ProrokWielki/Wooden-Clock/Hardware/Electronics/Schematic/ButtonBoard/ButtonBoard.kicad_sch

## KiCad design Hardware/Electronics/Schematic/ButtonBoard/ButtonBoard.kicad_sch (2025-12-02)

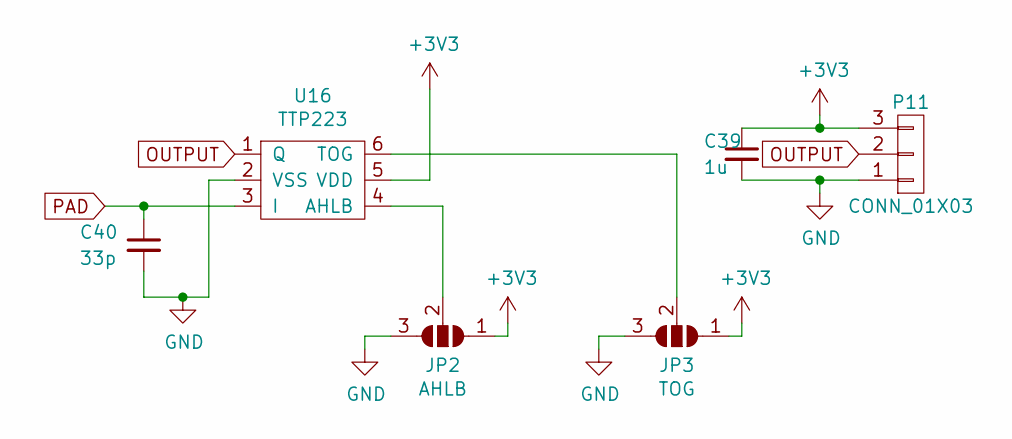
[picture p11: schematic ButtonBoard.kicad_sch]

Parts:
C39: 1u; C_0402_1005Metric
C40: 33p; C_0402_1005Metric
JP2: AHLB; SolderJumper-3_P1.3mm_Open_RoundedPad1.0x1.5mm
JP3: TOG; SolderJumper-3_P1.3mm_Open_RoundedPad1.0x1.5mm
P11: CONN_01X03; Molex_CLIK-Mate_502382-0370_1x03-1MP_P1.25mm_Vertical
U16: TTP223; SOT-23-6

Connections:
+3V3: C39.1, JP2.1 (A), JP3.1 (A), P11.3, U16.5 (VDD)
GND: C39.2, C40.2, JP2.3 (B), JP3.3 (B), P11.1, U16.2 (VSS)
unnamed: JP2.2 (C), U16.4 (AHLB)
unnamed: JP3.2 (C), U16.6 (TOG)
OUTPUT: P11.2, U16.1 (Q)
PAD: C40.1, U16.3 (I)
