ProrokWielki/Wooden-Clock/Hardware/Electronics/Schematic/DisplayBoard/DisplayBoard.kicad_sch

## KiCad design Hardware/Electronics/Schematic/DisplayBoard/DisplayBoard.kicad_sch (2025-12-02)

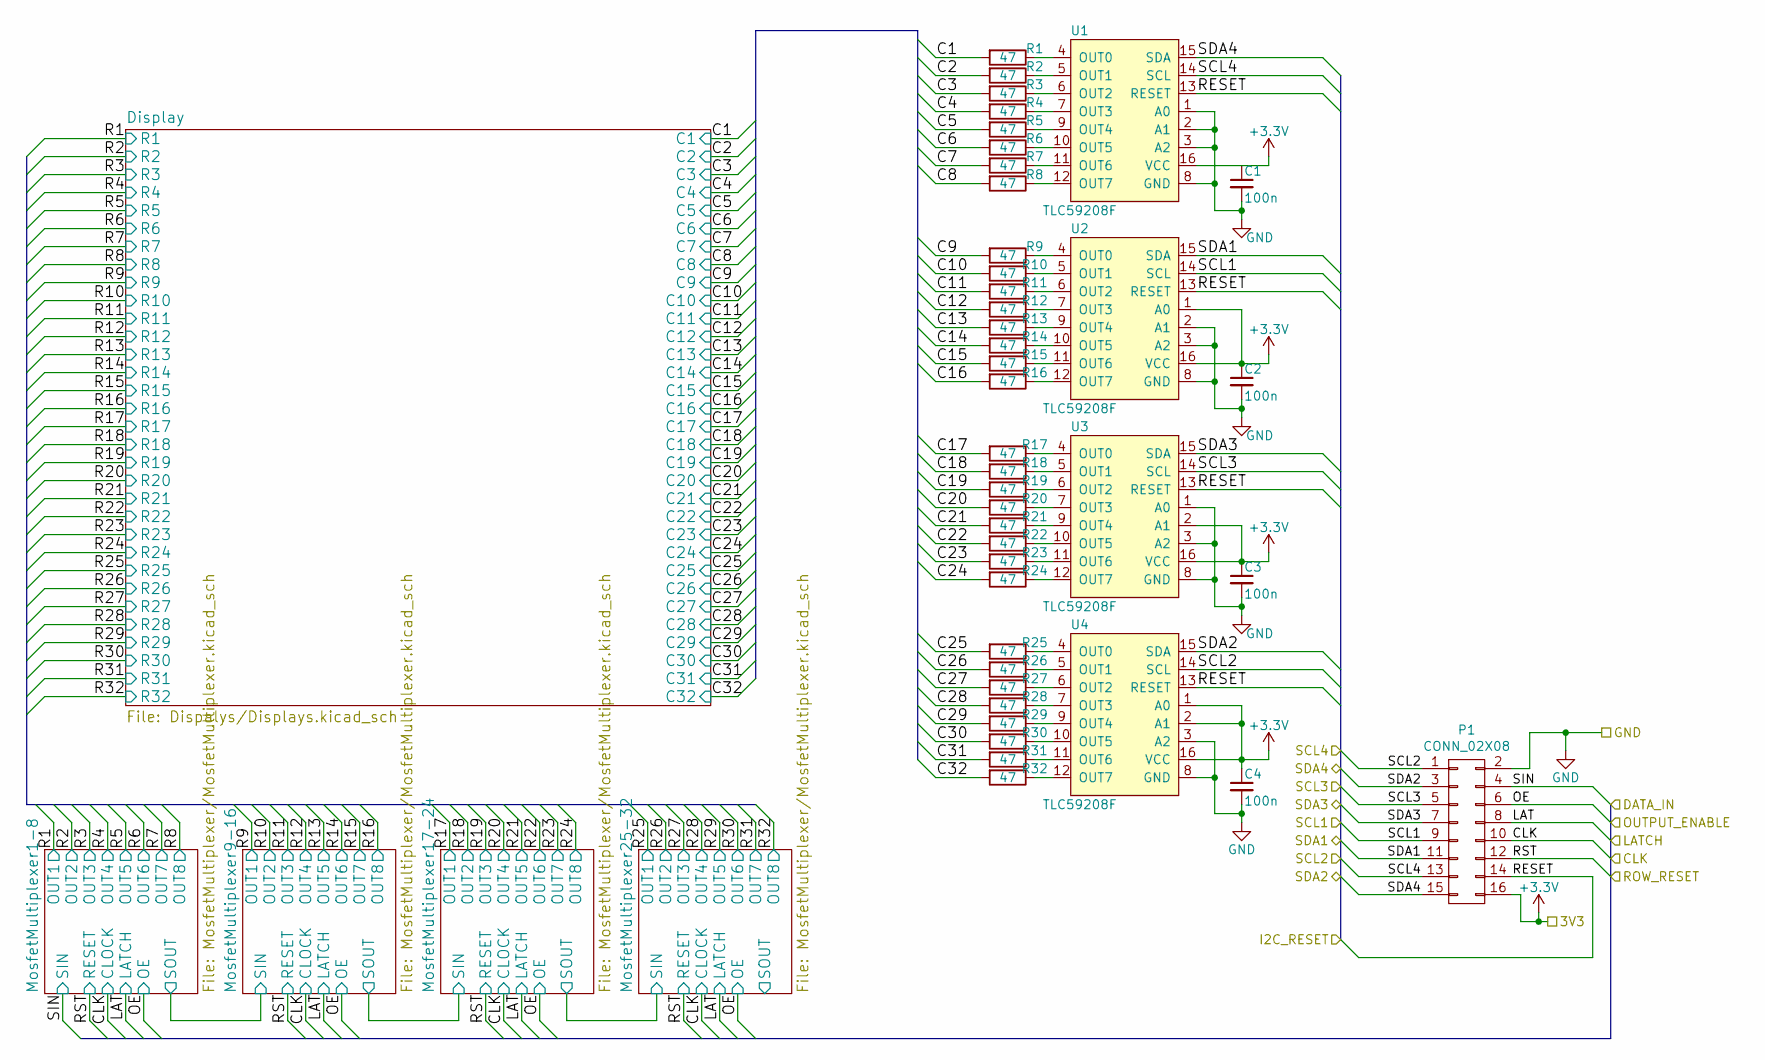
[picture p12: schematic DisplayBoard.kicad_sch]

Parts:
C1, C2, C3, C4: 100n; C_0402_NoSilk
P1: CONN_02X08; Pin_Header_Straight_2x08_Pitch2.54mm_SMD
R1, R2, R3, R4, R5, R6, R7, R8, R9, R10, R11, R12, R13, R14, R15, R16, R17, R18, R19, R20, R21, R22, R23, R24, R25, R26, R27, R28, R29, R30, R31, R32: 47; R_0805_HandSoldering
U1, U2, U3, U4: TLC59208F; TSSOP16

Connections:
+3.3V: C2.1, C3.1, C4.1, P1.16, U1.16 (VCC), U2.1 (A0), U2.16 (VCC), U3.2 (A1), U3.16 (VCC), U4.1 (A0), U4.2 (A1), U4.16 (VCC)
C1: R1.2
C2: R2.2
C3: R3.2
C4: R4.2
C5: R5.2
C6: R6.2
C7: R7.2
C8: R8.2
C9: R9.2
C10: R10.2
C11: R11.2
C12: R12.2
C13: R13.2
C14: R14.2
C15: R15.2
C16: R16.2
C17: R17.2
C18: R18.2
C19: R19.2
C20: R20.2
C21: R21.2
C22: R22.2
C23: R23.2
C24: R24.2
C25: R25.2
C26: R26.2
C27: R27.2
C28: R28.2
C29: R29.2
C30: R30.2
C31: R31.2
C32: R32.2
CLK: P1.10
GND: C1.2, C2.2, C3.2, C4.2, P1.2, U1.1 (A0), U1.2 (A1), U1.3 (A2), U1.8 (GND), U2.2 (A1), U2.3 (A2), U2.8 (GND), U3.1 (A0), U3.3 (A2), U3.8 (GND), U4.3 (A2), U4.8 (GND)
LAT: P1.8
unnamed: R1.1, U1.4 (OUT0)
unnamed: R2.1, U1.5 (OUT1)
unnamed: R3.1, U1.6 (OUT2)
unnamed: R4.1, U1.7 (OUT3)
unnamed: R5.1, U1.9 (OUT4)
unnamed: R6.1, U1.10 (OUT5)
unnamed: R7.1, U1.11 (OUT6)
unnamed: R8.1, U1.12 (OUT7)
unnamed: R9.1, U2.4 (OUT0)
unnamed: R10.1, U2.5 (OUT1)
unnamed: R11.1, U2.6 (OUT2)
unnamed: R12.1, U2.7 (OUT3)
unnamed: R13.1, U2.9 (OUT4)
unnamed: R14.1, U2.10 (OUT5)
unnamed: R15.1, U2.11 (OUT6)
unnamed: R16.1, U2.12 (OUT7)
unnamed: R17.1, U3.4 (OUT0)
unnamed: R18.1, U3.5 (OUT1)
unnamed: R19.1, U3.6 (OUT2)
unnamed: R20.1, U3.7 (OUT3)
unnamed: R21.1, U3.9 (OUT4)
unnamed: R22.1, U3.10 (OUT5)
unnamed: R23.1, U3.11 (OUT6)
unnamed: R24.1, U3.12 (OUT7)
unnamed: R25.1, U4.4 (OUT0)
unnamed: R26.1, U4.5 (OUT1)
unnamed: R27.1, U4.6 (OUT2)
unnamed: R28.1, U4.7 (OUT3)
unnamed: R29.1, U4.9 (OUT4)
unnamed: R30.1, U4.10 (OUT5)
unnamed: R31.1, U4.11 (OUT6)
unnamed: R32.1, U4.12 (OUT7)
OE: P1.6
RESET: P1.14, U1.13 (RESET), U2.13 (RESET), U3.13 (RESET), U4.13 (RESET)
RST: P1.12
SCL1: P1.9, U2.14 (SCL)
SCL2: P1.1, U4.14 (SCL)
SCL3: P1.5, U3.14 (SCL)
SCL4: P1.13, U1.14 (SCL)
SDA1: P1.11, U2.15 (SDA)
SDA2: P1.3, U4.15 (SDA)
SDA3: P1.7, U3.15 (SDA)
SDA4: P1.15, U1.15 (SDA)
SIN: P1.4
