ProrokWielki/Wooden-Clock/Hardware/Electronics/Schematic/MainBoard/MainBoard.kicad_sch

## KiCad design Hardware/Electronics/Schematic/MainBoard/MainBoard.kicad_sch (2025-12-02)

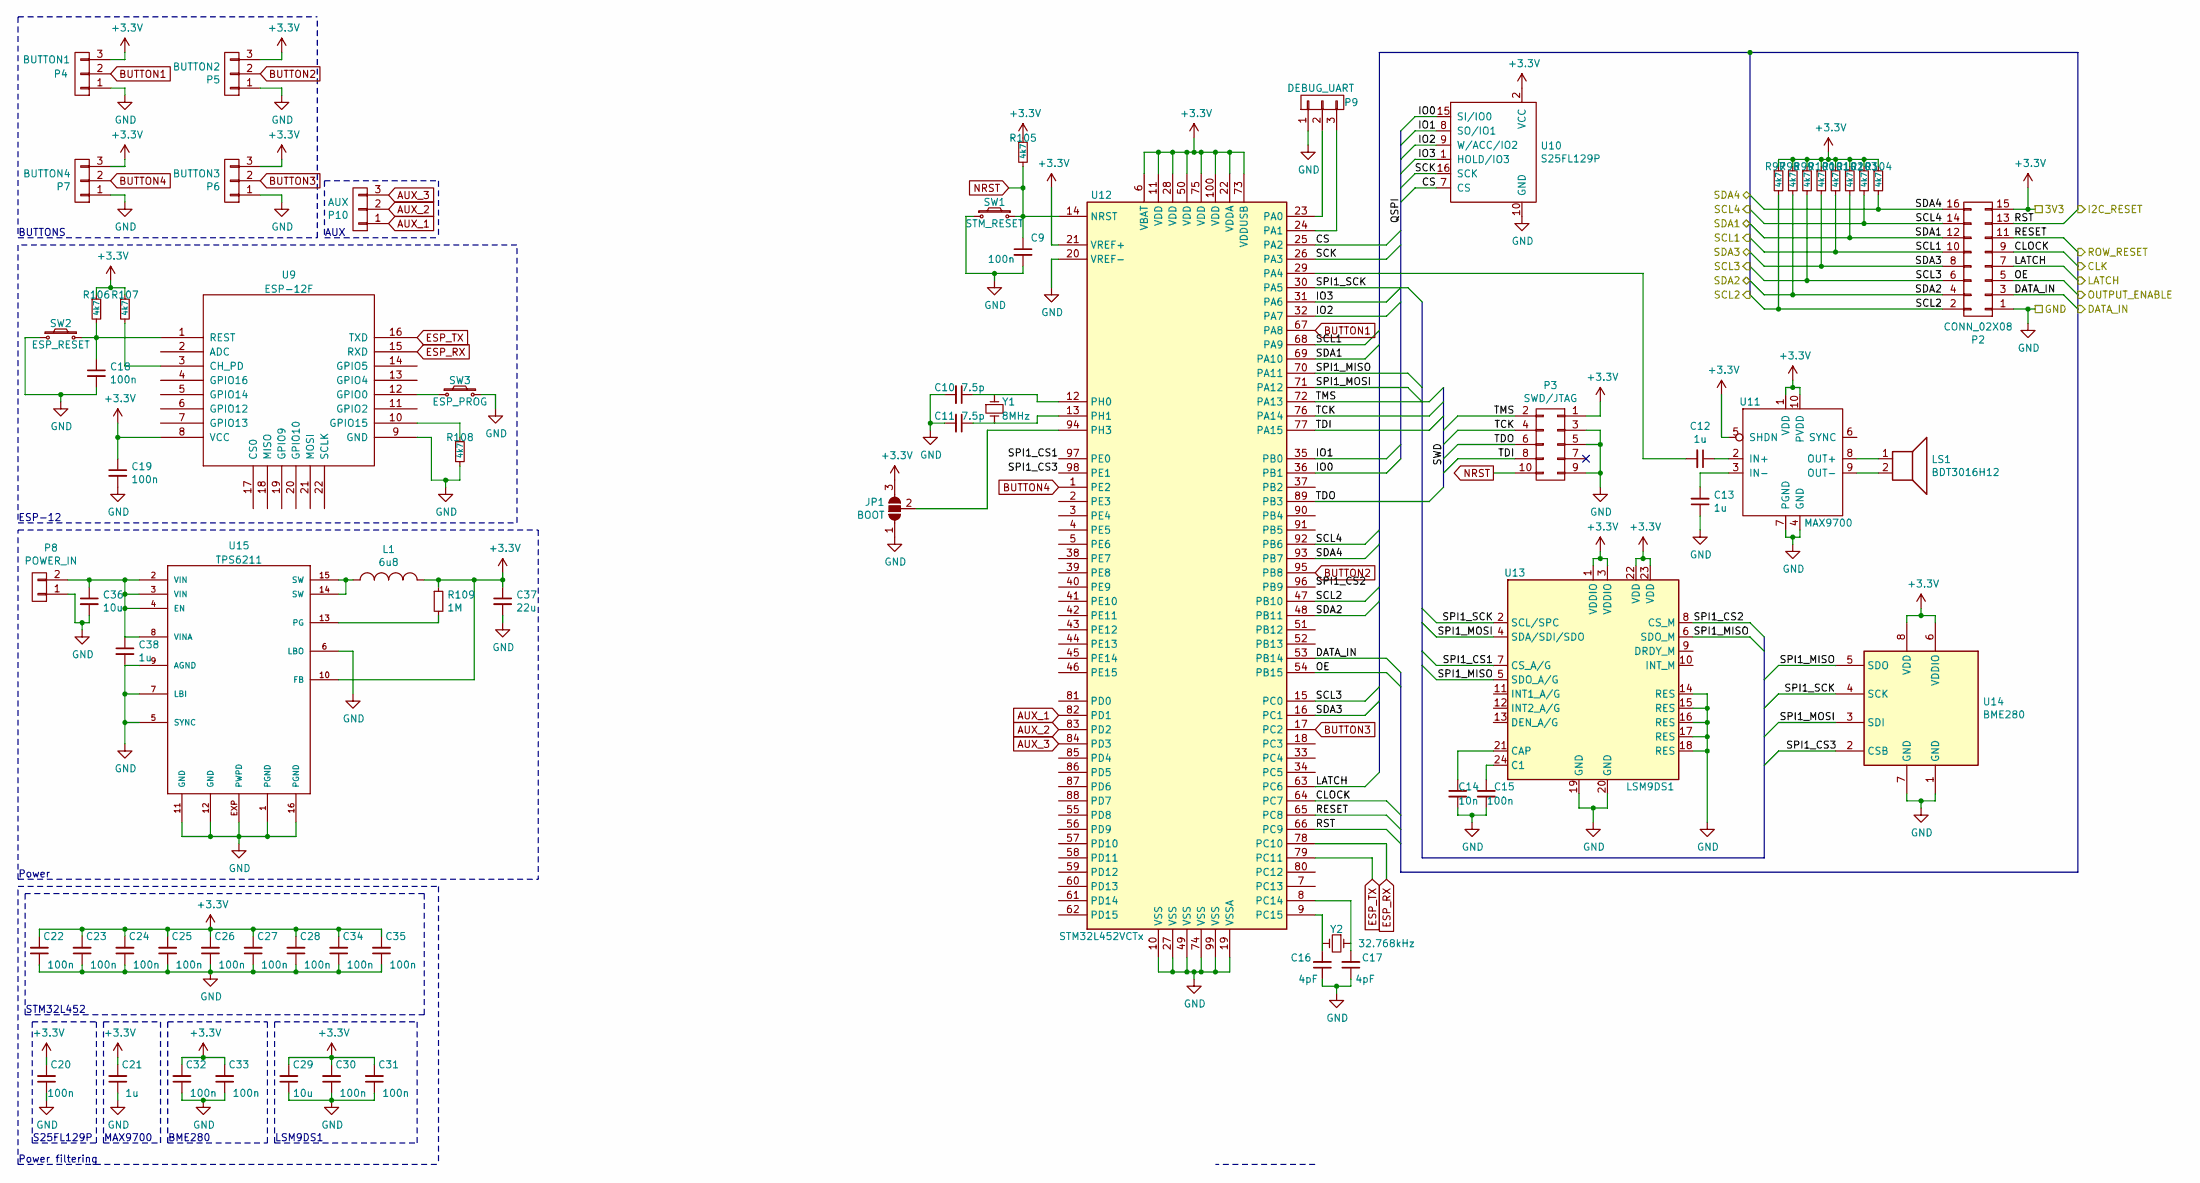
[picture p13: schematic MainBoard.kicad_sch]

Parts:
C9, C15, C18, C19, C20, C22, C23, C24, C25, C26, C27, C28, C30, C31, C32, C33, C34, C35: 100n; C_0402_NoSilk
C10, C11: 7.5p; C_0402_NoSilk
C12, C13, C21, C38: 1u; C_0402_NoSilk
C14: 10n; C_0402_NoSilk
C16, C17: 4pF; C_0402_NoSilk
C29: 10u; C_0402_NoSilk
C36: 10u; C_0805_2012Metric_Pad1.15x1.40mm_HandSolder
C37: 22u; C_1206_3216Metric_Pad1.42x1.75mm_HandSolder
JP1: BOOT; SolderJumper-3_P1.3mm_Open_RoundedPad1.0x1.5mm
L1: 6u8; L_Coilcraft_XxL4040
LS1: BDT3016H12
P2: CONN_02X08; Pin_Header_Straight_2x08_Pitch2.54mm_SMD
P3: SWD/JTAG; SAMTEC-TSM-105-01-X-DH
P4: BUTTON1; Molex_CLIK-Mate_502386-0370_1x03-1MP_P1.25mm_Horizontal
P5: BUTTON2; Molex_CLIK-Mate_502386-0370_1x03-1MP_P1.25mm_Horizontal
P6: BUTTON3; Molex_CLIK-Mate_502386-0370_1x03-1MP_P1.25mm_Horizontal
P7: BUTTON4; Molex_CLIK-Mate_502386-0370_1x03-1MP_P1.25mm_Horizontal
P8: POWER_IN; Molex_CLIK-Mate_502382-0270_1x02-1MP_P1.25mm_Vertical
P9: DEBUG_UART; Harwin_M20-89003xx_1x03_P2.54mm_Horizontal
P10: AUX; Molex_CLIK-Mate_502386-0370_1x03-1MP_P1.25mm_Horizontal
R97, R98, R99, R100, R101, R102, R103, R104, R105, R106, R107, R108: 4k7; R_0805_2012Metric_Pad1.15x1.40mm_HandSolder
R109: 1M; C_0805_2012Metric_Pad1.15x1.40mm_HandSolder
SW1: STM_RESET; E-switch_6x6mm
SW2: ESP_RESET; E-switch_6x6mm
SW3: ESP_PROG; E-switch_6x6mm
U9: ESP-12F
U10: S25FL129P; SOIC-16W_7.5x10.3mm_P1.27mm
U11: MAX9700; MSOP10-0.5
U12: STM32L452VCTx; LQFP-100_14x14mm_P0.5mm
U13: LSM9DS1; LGA-24L_3x3.5mm_P0.43mm
U14: BME280; Bosch_LGA-8_2.5x2.5mm_P0.65mm_ClockwisePinNumbering
U15: TPS6211; QFN16-4X4
Y1: 8MHz; Crystal_SMD_Abracon_ABM3-2Pin_5.0x3.2mm_HandSoldering
Y2: 32.768kHz; Crystal_SMD_MicroCrystal_CC7V-T1A-2Pin_3.2x1.5mm_HandSolder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

Connections:
+3.3V: C19.1, C20.2, C21.2, C22.2, C23.2, C24.2, C25.2, C26.2, C27.2, C28.2, C29.2, C30.2, C31.2, C32.2, C33.2, C34.2, C35.2, C37.1, JP1.3 (B), L1.2, P2.15, P3.1, P4.3, P5.3, P6.3, P7.3, R97.1, R98.1, R99.1, R100.1, R101.1, R102.1, R103.1, R104.1, R105.1, R106.1, R107.1, R109.1, U9.8 (VCC), U10.2 (VCC), U11.1 (VDD), U11.5 (SHDN), U11.10 (PVDD), U12.6 (VBAT), U12.11 (VDD), U12.21 (VREF+), U12.22 (VDDA), U12.28 (VDD), U12.50 (VDD), U12.73 (VDDUSB), U12.75 (VDD), U12.100 (VDD), U13.1 (VDDIO), U13.3 (VDDIO), U13.22 (VDD), U13.23 (VDD), U14.6 (VDDIO), U14.8 (VDD), U15.10 (FB)
AUX_1: P10.1, U12.82 (PD1)
AUX_2: P10.2, U12.83 (PD2)
AUX_3: P10.3, U12.84 (PD3)
BUTTON1: P4.2, U12.67 (PA8)
BUTTON2: P5.2, U12.95 (PB8)
BUTTON3: P6.2, U12.17 (PC2)
BUTTON4: P7.2, U12.1 (PE2)
CLOCK: P2.9, U12.64 (PC7)
CS: U10.7 (CS), U12.25 (PA2)
DATA_IN: P2.3, U12.53 (PB14)
ESP_RX: U9.15 (RXD), U12.78 (PC10)
ESP_TX: U9.16 (TXD), U12.79 (PC11)
GND: C9.2, C10.2, C11.2, C13.1, C14.2, C15.2, C16.1, C17.1, C18.2, C19.2, C20.1, C21.1, C22.1, C23.1, C24.1, C25.1, C26.1, C27.1, C28.1, C29.1, C30.1, C31.1, C32.1, C33.1, C34.1, C35.1, C36.2, C37.2, C38.2, JP1.1 (A), P2.1, P3.3, P3.5, P3.9, P4.1, P5.1, P6.1, P7.1, P8.1, P9.1, R108.2, SW1.1, SW2.1, SW3.2, U9.9 (GND), U10.10 (GND), U11.4 (GND), U11.7 (PGND), U12.10 (VSS), U12.19 (VSSA), U12.20 (VREF-), U12.27 (VSS), U12.49 (VSS), U12.74 (VSS), U12.99 (VSS), U13.14 (RES), U13.15 (RES), U13.16 (RES), U13.17 (RES), U13.18 (RES), U13.19 (GND), U13.20 (GND), U14.1 (GND), U14.7 (GND), U15.1 (PGND), U15.5 (SYNC), U15.6 (LBO), U15.7 (LBI), U15.9 (AGND), U15.11 (GND), U15.12 (GND), U15.16 (PGND), U15.EXP (PWPD)
IO0: U10.15 (SI/IO0), U12.36 (PB1)
IO1: U10.8 (SO/IO1), U12.35 (PB0)
IO2: U10.9 (W/ACC/IO2), U12.32 (PA7)
IO3: U10.1 (HOLD/IO3), U12.31 (PA6)
LATCH: P2.7, U12.63 (PC6)
NRST: C9.1, P3.10, R105.2, SW1.2, U12.14 (NRST)
unnamed: C10.1, U12.12 (PH0)
unnamed: C11.1, U12.13 (PH1)
unnamed: C12.1, U11.2 (IN+)
unnamed: C12.2, U12.29 (PA4)
unnamed: C13.2, U11.3 (IN-)
unnamed: C14.1, U13.21 (CAP)
unnamed: C15.1, U13.24 (C1)
unnamed: C16.2, U12.9 (PC15)
unnamed: C17.2, U12.8 (PC14)
unnamed: C18.1, R106.2, SW2.2, U9.1 (REST)
unnamed: C36.1, C38.1, P8.2, U15.2 (VIN), U15.3 (VIN), U15.4 (EN), U15.8 (VINA)
unnamed: JP1.2 (C), U12.94 (PH3)
unnamed: L1.1, U15.14 (SW), U15.15 (SW)
unnamed: LS1.1, U11.8 (OUT+)
unnamed: LS1.2, U11.9 (OUT-)
unnamed: P9.2, U12.23 (PA0)
unnamed: P9.3, U12.24 (PA1)
unnamed: R107.2, U9.3 (CH_PD)
unnamed: R108.1, U9.10 (GPIO15)
unnamed: R109.2, U15.13 (PG)
unnamed: SW3.1, U9.12 (GPIO0)
OE: P2.5, U12.54 (PB15)
RESET: P2.11, U12.65 (PC8)
RST: P2.13, U12.66 (PC9)
SCK: U10.16 (SCK), U12.26 (PA3)
SCL1: P2.10, R101.2, U12.68 (PA9)
SCL2: P2.2, R97.2, U12.47 (PB10)
SCL3: P2.6, R99.2, U12.15 (PC0)
SCL4: P2.14, R103.2, U12.92 (PB6)
SDA1: P2.12, R102.2, U12.69 (PA10)
SDA2: P2.4, R98.2, U12.48 (PB11)
SDA3: P2.8, R100.2, U12.16 (PC1)
SDA4: P2.16, R104.2, U12.93 (PB7)
SPI1_CS1: U12.97 (PE0), U13.7 (CS_A/G)
SPI1_CS2: U12.96 (PB9), U13.8 (CS_M)
SPI1_CS3: U12.98 (PE1), U14.2 (CSB)
SPI1_MISO: U12.70 (PA11), U13.5 (SDO_A/G), U13.6 (SDO_M), U14.5 (SDO)
SPI1_MOSI: U12.71 (PA12), U13.4 (SDA/SDI/SDO), U14.3 (SDI)
SPI1_SCK: U12.30 (PA5), U13.2 (SCL/SPC), U14.4 (SCK)
TCK: P3.4, U12.76 (PA14)
TDI: P3.8, U12.77 (PA15)
TDO: P3.6, U12.89 (PB3)
TMS: P3.2, U12.72 (PA13)

Notes on the sheet:
Power
BUTTONS
AUX
S25FL129P
Power filtering
BME280
LSM9DS1
STM32L452
ESP-12
MAX9700
