ProrokWielki/Wooden-Clock/Hardware/Electronics/Schematic/DisplayBoard/Dispalys/Displays.kicad_sch

## KiCad design Hardware/Electronics/Schematic/DisplayBoard/Dispalys/Displays.kicad_sch (2025-12-02)

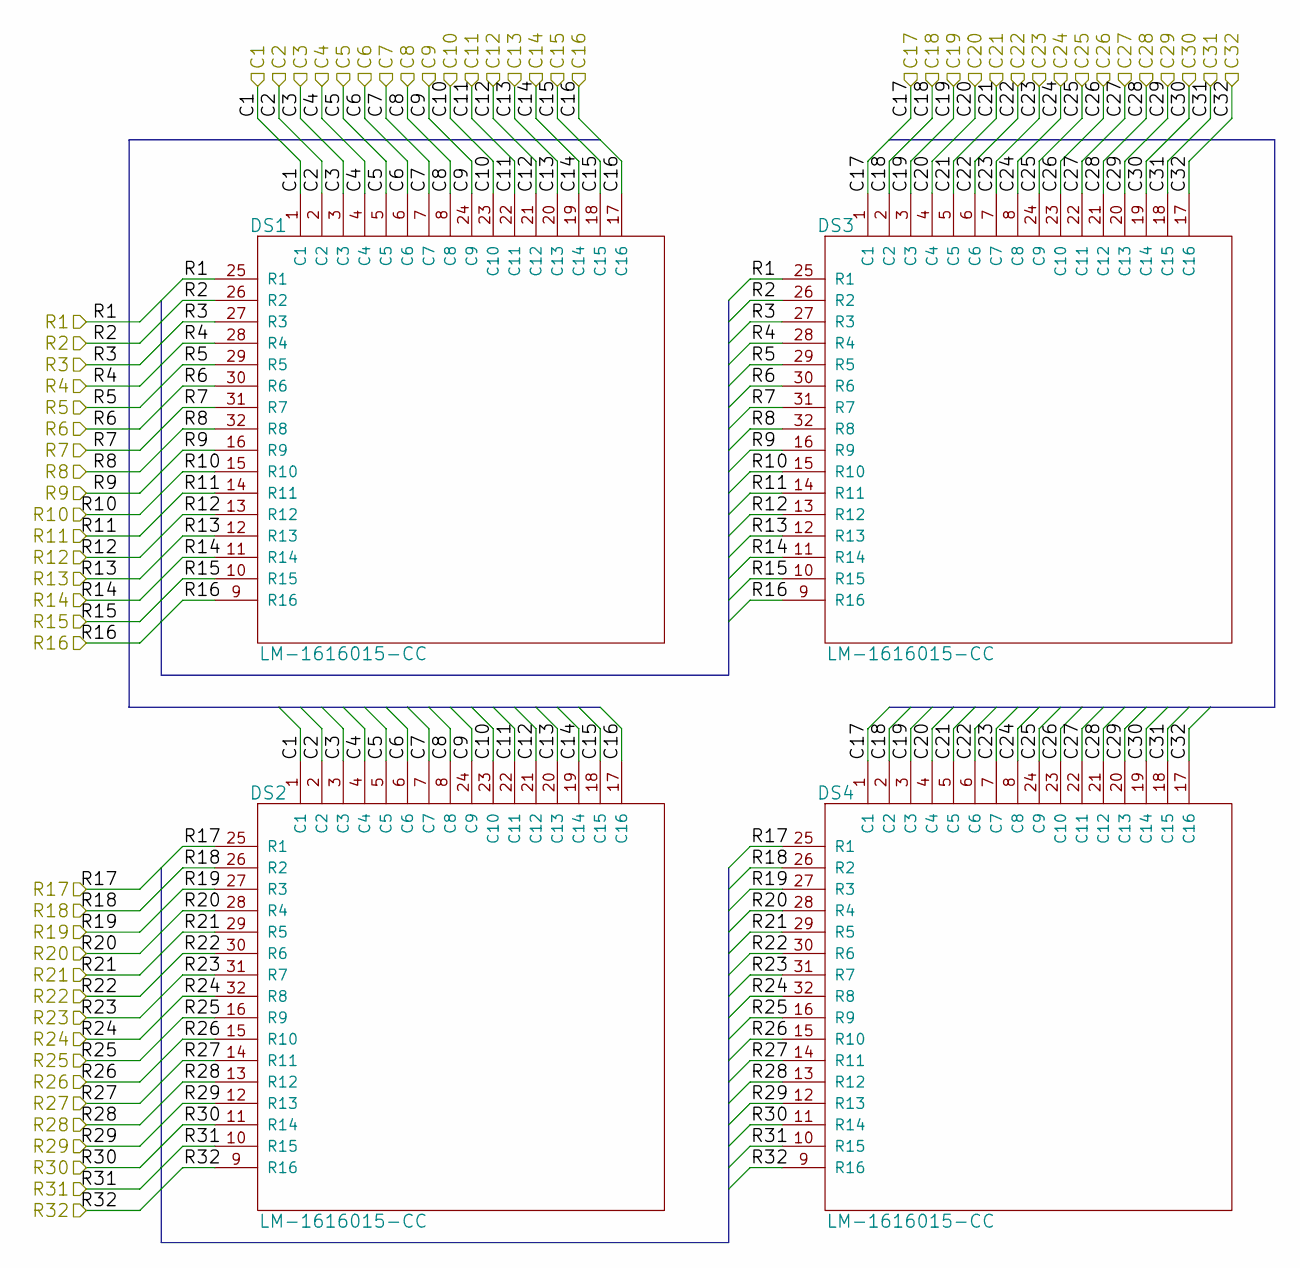
[picture p14: schematic Displays.kicad_sch]

Parts:
DS1, DS2, DS3, DS4: LM-1616015-CC; LM1616X15

Connections:
C1: DS1.1 (C1), DS2.1 (C1)
C2: DS1.2 (C2), DS2.2 (C2)
C3: DS1.3 (C3), DS2.3 (C3)
C4: DS1.4 (C4), DS2.4 (C4)
C5: DS1.5 (C5), DS2.5 (C5)
C6: DS1.6 (C6), DS2.6 (C6)
C7: DS1.7 (C7), DS2.7 (C7)
C8: DS1.8 (C8), DS2.8 (C8)
C9: DS1.24 (C9), DS2.24 (C9)
C10: DS1.23 (C10), DS2.23 (C10)
C11: DS1.22 (C11), DS2.22 (C11)
C12: DS1.21 (C12), DS2.21 (C12)
C13: DS1.20 (C13), DS2.20 (C13)
C14: DS1.19 (C14), DS2.19 (C14)
C15: DS1.18 (C15), DS2.18 (C15)
C16: DS1.17 (C16), DS2.17 (C16)
C17: DS3.1 (C1), DS4.1 (C1)
C18: DS3.2 (C2), DS4.2 (C2)
C19: DS3.3 (C3), DS4.3 (C3)
C20: DS3.4 (C4), DS4.4 (C4)
C21: DS3.5 (C5), DS4.5 (C5)
C22: DS3.6 (C6), DS4.6 (C6)
C23: DS3.7 (C7), DS4.7 (C7)
C24: DS3.8 (C8), DS4.8 (C8)
C25: DS3.24 (C9), DS4.24 (C9)
C26: DS3.23 (C10), DS4.23 (C10)
C27: DS3.22 (C11), DS4.22 (C11)
C28: DS3.21 (C12), DS4.21 (C12)
C29: DS3.20 (C13), DS4.20 (C13)
C30: DS3.19 (C14), DS4.19 (C14)
C31: DS3.18 (C15), DS4.18 (C15)
C32: DS3.17 (C16), DS4.17 (C16)
R1: DS1.25 (R1), DS3.25 (R1)
R2: DS1.26 (R2), DS3.26 (R2)
R3: DS1.27 (R3), DS3.27 (R3)
R4: DS1.28 (R4), DS3.28 (R4)
R5: DS1.29 (R5), DS3.29 (R5)
R6: DS1.30 (R6), DS3.30 (R6)
R7: DS1.31 (R7), DS3.31 (R7)
R8: DS1.32 (R8), DS3.32 (R8)
R9: DS1.16 (R9), DS3.16 (R9)
R10: DS1.15 (R10), DS3.15 (R10)
R11: DS1.14 (R11), DS3.14 (R11)
R12: DS1.13 (R12), DS3.13 (R12)
R13: DS1.12 (R13), DS3.12 (R13)
R14: DS1.11 (R14), DS3.11 (R14)
R15: DS1.10 (R15), DS3.10 (R15)
R16: DS1.9 (R16), DS3.9 (R16)
R17: DS2.25 (R1), DS4.25 (R1)
R18: DS2.26 (R2), DS4.26 (R2)
R19: DS2.27 (R3), DS4.27 (R3)
R20: DS2.28 (R4), DS4.28 (R4)
R21: DS2.29 (R5), DS4.29 (R5)
R22: DS2.30 (R6), DS4.30 (R6)
R23: DS2.31 (R7), DS4.31 (R7)
R24: DS2.32 (R8), DS4.32 (R8)
R25: DS2.16 (R9), DS4.16 (R9)
R26: DS2.15 (R10), DS4.15 (R10)
R27: DS2.14 (R11), DS4.14 (R11)
R28: DS2.13 (R12), DS4.13 (R12)
R29: DS2.12 (R13), DS4.12 (R13)
R30: DS2.11 (R14), DS4.11 (R14)
R31: DS2.10 (R15), DS4.10 (R15)
R32: DS2.9 (R16), DS4.9 (R16)
