ProrokWielki/Wooden-Clock/Hardware/Electronics/Schematic/DisplayBoard/MosfetMultiplexer/MosfetMultiplexer.kicad_sch

## KiCad design Hardware/Electronics/Schematic/DisplayBoard/MosfetMultiplexer/MosfetMultiplexer.kicad_sch (2025-12-02)

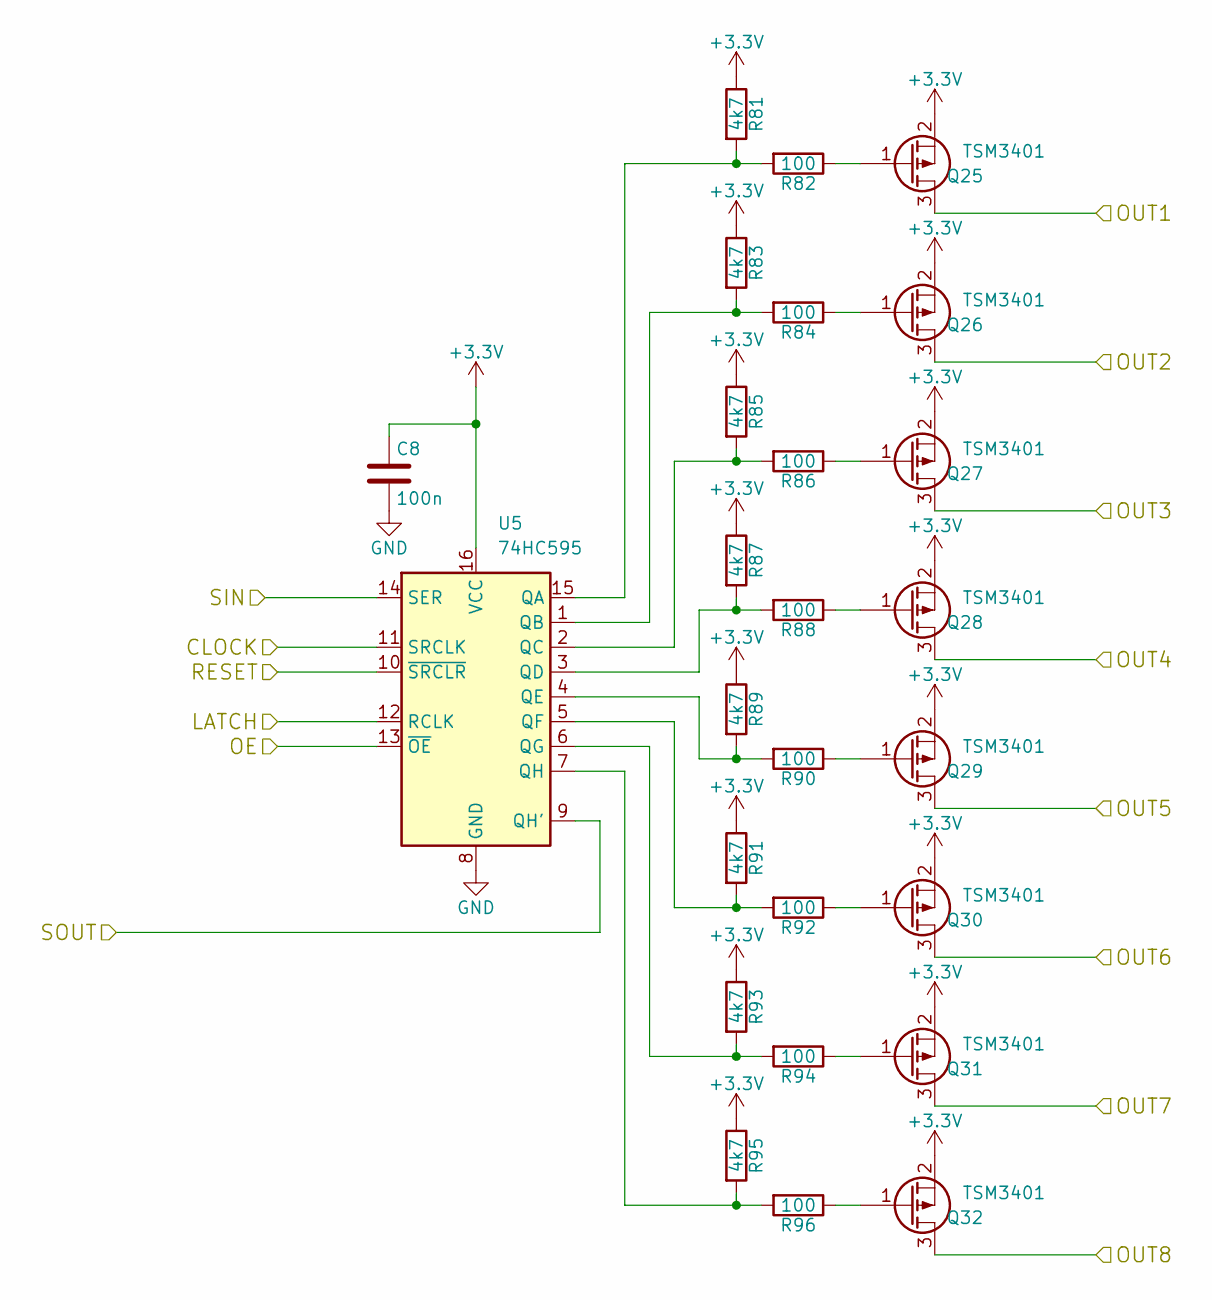
[picture p15: schematic MosfetMultiplexer.kicad_sch]

Parts:
C8: 100n; C_0402_NoSilk
Q25, Q26, Q27, Q28, Q29, Q30, Q31, Q32: TSM3401; SOT23-3
R81, R83, R85, R87, R89, R91, R93, R95: 4k7; R_0805_HandSoldering
R82, R84, R86, R88, R90, R92, R94, R96: 100; R_0805_HandSoldering
U5: 74HC595

Connections:
+3.3V: C8.1, Q25.2 (S), Q26.2 (S), Q27.2 (S), Q28.2 (S), Q29.2 (S), Q30.2 (S), Q31.2 (S), Q32.2 (S), R81.1, R83.1, R85.1, R87.1, R89.1, R91.1, R93.1, R95.1, U5.16 (VCC)
CLOCK: U5.11 (SRCLK)
GND: C8.2, U5.8 (GND)
LATCH: U5.12 (RCLK)
unnamed: Q25.1 (G), R82.1
unnamed: Q26.1 (G), R84.1
unnamed: Q27.1 (G), R86.1
unnamed: Q28.1 (G), R88.1
unnamed: Q29.1 (G), R90.1
unnamed: Q30.1 (G), R92.1
unnamed: Q31.1 (G), R94.1
unnamed: Q32.1 (G), R96.1
unnamed: R81.2, R82.2, U5.15 (QA)
unnamed: R83.2, R84.2, U5.1 (QB)
unnamed: R85.2, R86.2, U5.2 (QC)
unnamed: R87.2, R88.2, U5.3 (QD)
unnamed: R89.2, R90.2, U5.4 (QE)
unnamed: R91.2, R92.2, U5.5 (QF)
unnamed: R93.2, R94.2, U5.6 (QG)
unnamed: R95.2, R96.2, U5.7 (QH)
OE: U5.13 (~OE)
OUT1: Q25.3 (D)
OUT2: Q26.3 (D)
OUT3: Q27.3 (D)
OUT4: Q28.3 (D)
OUT5: Q29.3 (D)
OUT6: Q30.3 (D)
OUT7: Q31.3 (D)
OUT8: Q32.3 (D)
RESET: U5.10 (~SRCLR)
SIN: U5.14 (SER)
SOUT: U5.9 (QH')
