ProrokWielki/Wooden-Clock/Software/STM/src/APP/Screens/StateArrows.hpp

/**
 * StateArrows.hpp
 *
 *  Created on: 10-03-2019
 *  @author: Paweł Warzecha
 */

#ifndef APP_STATEMACHINE_STATES_STATEARROWS_HPP_
#define APP_STATEMACHINE_STATES_STATEARROWS_HPP_

#include <Canvas.hpp>

#include "../Assets/Images/Images.hpp"
#include "Assets/Animations/Animations.hpp"
#include "Widget.hpp"
#include <BSP/BSP.hpp>
#include <array>
#include <functional>
#include <widgets/Animation.hpp>

class StateArrows: public Canvas
{
public:
    /**
     * @brief Constructor.
     */
    StateArrows() : arrows{get_animation(AnimationType::ARROWS)}
    {
    }

    /**
     * @brief Execution of the State action.
     */
    void init() override
    {
        static const WidgetAndPositions arr{.x = 0, .y = 0, .widget = arrows};
        static const std::array<const std::reference_wrapper<const WidgetAndPositions>, 1> widgets{arr};
        add(widgets);
        // validate();
    }

    void up_date() override
    {
    }

private:
    Animation & arrows;
};

#endif /* APP_STATEMACHINE_STATES_STATEARROWS_HPP_ */
