ProrokWielki/Wooden-Clock/Software/HAL/HAL.cpp

/*
 * HAL.cpp
 *
 *  Created on: 21-11-2018
 *      Author: Paweł Warzecha
 */

#include "HAL.hpp"

#include <stm32l4xx.h>

GPIO HAL::I2C1_SCL(GPIOA, 9);
GPIO HAL::I2C1_SDA(GPIOA, 10);

GPIO HAL::I2C2_SCL(GPIOB, 10);
GPIO HAL::I2C2_SDA(GPIOB, 11);

GPIO HAL::I2C3_SCL(GPIOC, 0);
GPIO HAL::I2C3_SDA(GPIOC, 1);

GPIO HAL::I2C4_SCL(GPIOB, 6);
GPIO HAL::I2C4_SDA(GPIOB, 7);

GPIO HAL::SPI1_MISO(GPIOA, 11);
GPIO HAL::SPI1_MOSI(GPIOA, 12);
GPIO HAL::SPI1_SCK(GPIOA, 5);
GPIO HAL::SPI1_CS1(GPIOE, 0);
GPIO HAL::SPI1_CS2(GPIOB, 9);
GPIO HAL::SPI1_CS3(GPIOE, 1);

GPIO HAL::QSPI_IO0(GPIOB, 1);
GPIO HAL::QSPI_IO1(GPIOB, 0);
GPIO HAL::QSPI_IO2(GPIOA, 7);
GPIO HAL::QSPI_IO3(GPIOA, 6);
GPIO HAL::QSPI_CLK(GPIOA, 3);
GPIO HAL::QSPI_CS(GPIOA, 2);

GPIO HAL::UART3_TX(GPIOC, 10);
GPIO HAL::UART3_RX(GPIOC, 11);

GPIO HAL::UART4_TX(GPIOA, 0);
GPIO HAL::UART4_RX(GPIOA, 1);

GPIO HAL::TLC_RESET(GPIOC, 9);

GPIO HAL::SR_DATAIN(GPIOB, 14);
GPIO HAL::SR_RCLOCK(GPIOC, 7);
GPIO HAL::SR_SCLOCK(GPIOC, 6);
GPIO HAL::SR_OE(GPIOB, 15);
GPIO HAL::SR_CLEAR(GPIOC, 8);

GPIO HAL::BUTTON1(GPIOA, 8);
GPIO HAL::BUTTON2(GPIOB, 8);
GPIO HAL::BUTTON3(GPIOC, 2);
GPIO HAL::BUTTON4(GPIOE, 2);

DMA HAL::DMA1_2(DMA1, DMA1_Channel2, 2);
DMA HAL::DMA1_4(DMA1, DMA1_Channel4, 4);
DMA HAL::DMA2_2(DMA2, DMA2_Channel2, 2);
DMA HAL::DMA2_7(DMA2, DMA2_Channel7, 7);

DMA HAL::DMA2_4(DMA2, DMA2_Channel4, 4);

I2C HAL::I2C_1(I2C1, &DMA2_7);
I2C HAL::I2C_2(I2C2, &DMA1_4);
I2C HAL::I2C_3(I2C3, &DMA1_2);
I2C HAL::I2C_4(I2C4, &DMA2_2);

SPI HAL::SPI_1(SPI1);

SR_74HC595 HAL::SR_74HC595_1(SR_DATAIN, SR_RCLOCK, SR_SCLOCK, SR_OE, SR_CLEAR);

TLC59208F HAL::TLC59208F_4(I2C_2, 0x46, TLC_RESET);
TLC59208F HAL::TLC59208F_3(I2C_3, 0x44, TLC_RESET);
TLC59208F HAL::TLC59208F_2(I2C_1, 0x42, TLC_RESET);
TLC59208F HAL::TLC59208F_1(I2C_4, 0x40, TLC_RESET);

LSM9DS1 HAL::LSM9DS1_1(SPI_1, SPI1_CS1, SPI1_CS2);

BME280 HAL::BME280_1(SPI_1, SPI1_CS3);

Timer HAL::Timer2(TIM2);

bool HAL::up;
bool HAL::down;
bool HAL::left;
bool HAL::right;

void HAL::init()
{
    up = false;
    down = false;
    left = false;
    right = false;

    clock_init();
    SystemCoreClockUpdate();

    GPIO_Init();

    QSPI_init();

    Timer_init();
    DMA_init();
    I2C_init();
    SPI_init();

    uint8_t who_am_i_m;
    uint8_t who_am_i_g;

    TLC59208F_init();

    SR_74HC595_init();
    LSM9DS1_init();

    DMA2_CSELR->CSELR |= (5 << 24);
    DMA1_CSELR->CSELR |= ((3 << 12) | (3 << 4));

    TIM2->DIER |= (1 << 0);

    RCC->APB1ENR1 |= 1 << 18;

    USART3->BRR = 0xA0;
    USART3->CR1 = 0x2f;

    who_am_i_m = LSM9DS1_1.get_who_am_i_m();
    who_am_i_g = LSM9DS1_1.get_who_am_i_g();

    BME280_1.init();

    BME280_1.get_id();

    auto hum = BME280_1.get_humidity();
    auto temp = BME280_1.get_temperature();
    auto pressure = BME280_1.get_pressure();
}

void HAL::QSPI_init(void)
{

    RCC->AHB3ENR = 1 << 8;  // QSPI_EN

    QUADSPI->CR = 255 << 24;

    QUADSPI->DCR |= 24 << 16;  // FSIZE = 24  -- 16MB
    QUADSPI->DCR |= 1 << 8;    // nCS stays high for at least 8 cycles between Flash memory commands

    QUADSPI->CR |= QUADSPI_CR_EN;  // Enable

    ///////////////////////////

    uint32_t ccr, sr;

    uint32_t tmp;

    /* Configure automatic polling mode to wait for memory ready */

    QUADSPI->DLR = 647; /* use len-1 so 20 bytes is (20-1 == 19) */

    /* Commands are sent through CCR */
    tmp = 1 << 26; /* indirect read */
    tmp |= 0x9F;
    tmp |= 1 << 8;
    tmp |= 1 << 24;
    QUADSPI->CCR = tmp;

    /////////////////////////////////////
    int len;
    int max_len = 648;
    uint32_t buf[648];

    uint32_t * a = buf;

    len = 0;
    /* manually transfer data from the QSPI peripheral, this
     * loop runs while QUADSPI_SR_BUSY is set. It pulls 1 byte
     * at a time.
     */
    do
    {
        sr = QUADSPI->SR;
        if (sr & (1 << 2))
        {
            *a = QUADSPI->DR;
            a++;
            len++;
            if (len >= max_len)
            {
                break;
            }
        }
    } while (sr & (1 << 5));

    /// ///////////////////////////////

    //    print_status(QUADSPI_SR);
    //    printf("\nRead ID returned %d bytes\n", len);
    QUADSPI->FCR = 0x1f;

    /////////////////////////////////////////
#if 1
    ccr = 0x06;
    ccr |= 1 << 8;
    ccr |= 1 << 26;
    QUADSPI->CCR = ccr;
    do
    {
        sr = QUADSPI->SR;
    } while (sr & (1 << 5));
    QUADSPI->FCR = 0x1f; /* reset the flags */
    ///

    uint8_t buffer = 1;

    ccr = 0;
    /* adjusting this to 0 fixed the write issue. */
    ccr |= 0x02; /* write 256 bytes */
    /* For some reason 1-1-4 command */
    ccr |= 1 << 8;
    ccr |= 1 << 10;
    ccr |= 2 << 12; /* 24 bit address */
    ccr |= 1 << 24;
    QUADSPI->DLR = 255;
    QUADSPI->AR = 0;
    QUADSPI->CCR = ccr; /* go write a page */
    tmp = 0;
    do
    {
        sr = QUADSPI->SR;
        if (sr & (1 << 1))
        {
            break;
        }
        tmp++;
        QUADSPI->DR = buffer++;
    } while (QUADSPI->SR & (1 << 5));

    QUADSPI->FCR = 0x1f;
#else
    ccr = 0x06;
    ccr |= 1 << 8;
    ccr |= 1 << 26;
    QUADSPI->CCR = ccr;
    do
    {
        sr = QUADSPI->SR;
    } while (sr & (1 << 5));
    QUADSPI->FCR = 0x1f; /* reset the flags */

    ccr = 0xC7;
    ccr |= 1 << 8;
    ccr |= 1 << 26;
    QUADSPI->CCR = ccr;
    do
    {
        sr = QUADSPI->SR;
    } while (sr & (1 << 5));
    QUADSPI->FCR = 0x1f; /* reset the flags */
                         ///
    for (uint32_t dupa = 0; dupa < 0x3fffffff; dupa++)
    {
        (void)dupa;
    }
#endif

    /* Commands are sent through CCR */
    ccr = 0x03;
    ccr |= 1 << 8;
    ccr |= 2 << 18;
    ccr |= 1 << 10;
    ccr |= 2 << 12; /* 24 bit address */
    ccr |= 1 << 24;
    ccr |= 1 << 26;
    QUADSPI->DLR = 255;
    QUADSPI->CCR = ccr;
    QUADSPI->AR = 0;

    /////////////////////////////////////

    a = buf;

    len = 0;
    /* manually transfer data from the QSPI peripheral, this
     * loop runs while QUADSPI_SR_BUSY is set. It pulls 1 byte
     * at a time.
     */
    do
    {
        sr = QUADSPI->SR;
        if (sr & (1 << 2))
        {
            *a = QUADSPI->DR;
            a++;
            len++;
            if (len >= max_len)
            {
                break;
            }
        }
    } while (sr & (1 << 5));

    /// ///////////////////////////////

    //    print_status(QUADSPI_SR);
    //    printf("\nRead ID returned %d bytes\n", len);
    QUADSPI->FCR = 0x1f;

    /* Commands are sent through CCR */
    ccr = 0x03;
    ccr |= 1 << 8;
    ccr |= 1 << 10;
    ccr |= 2 << 12; /* 24 bit address */
    ccr |= 2 << 18;
    ccr |= 1 << 24;
    ccr |= 3 << 26;
    QUADSPI->CCR = ccr;
}

void HAL::clock_init(void)
{
    // M = 1
    // N = 10
    // R = 2
    // P = 7
    // Q = 2

    //  while((RCC->CR & RCC_CR_PLLRDY) == 0);

    FLASH->ACR |= FLASH_ACR_LATENCY_4WS;  // Latency set to 4 wait states
    FLASH->ACR |= FLASH_ACR_PRFTEN;       // Prefetch enable
    FLASH->ACR |= FLASH_ACR_DCEN;         // Data cashe enable
    FLASH->ACR |= FLASH_ACR_ICEN;         // Instruction cashe enable

    RCC->CR |= RCC_CR_HSEON;

    while ((RCC->CR & RCC_CR_HSERDY) == 0)
        ;

    RCC->PLLCFGR = (3 << 0) | (20 << 8) | (1 << 24);

    RCC->CR |= RCC_CR_PLLON;  // HSI turned on

    while ((RCC->CR & RCC_CR_PLLRDY) == 0)
        ;

    RCC->CFGR |= (3 << 0);
}

void HAL::I2C_init(void)
{
    RCC->CCIPR |= RCC_CCIPR_I2C1SEL_0;
    RCC->CCIPR |= RCC_CCIPR_I2C2SEL_0;
    RCC->CCIPR |= RCC_CCIPR_I2C3SEL_0;
    RCC->CCIPR2 |= RCC_CCIPR2_I2C4SEL_0;

    /* Clock enable */
    RCC->APB1ENR1 |= RCC_APB1ENR1_I2C1EN;  // Enable clock for I2C1
    RCC->APB1ENR1 |= RCC_APB1ENR1_I2C2EN;  // Enable clock for I2C2
    RCC->APB1ENR1 |= RCC_APB1ENR1_I2C3EN;  // Enable clock for I2C3
    RCC->APB1ENR2 |= RCC_APB1ENR2_I2C4EN;  // Enable clock for I2C4

    /* Fast-mode Plus enable */
    SYSCFG->CFGR1 |= SYSCFG_CFGR1_I2C1_FMP;  // Enable FM+ for I2C1
    SYSCFG->CFGR1 |= SYSCFG_CFGR1_I2C2_FMP;  // Enable FM+ for I2C2
    SYSCFG->CFGR1 |= SYSCFG_CFGR1_I2C3_FMP;  // Enable FM+ for I2C3
    SYSCFG->CFGR1 |= SYSCFG_CFGR1_I2C4_FMP;  // Enable FM+ for I2C4

    SYSCFG->CFGR1 |= SYSCFG_CFGR1_I2C_PB6_FMP |  // Enable FM+ on PB6
                     SYSCFG_CFGR1_I2C_PB7_FMP;   // Enable FM+ on PB7

    /* I2C set timing*/
    I2C_1.set_timing(4, 1, 0, 3, 6);
    I2C_2.set_timing(4, 1, 0, 3, 6);
    I2C_3.set_timing(4, 1, 0, 3, 6);
    I2C_4.set_timing(4, 1, 0, 3, 6);

    /* I2C periphery enable */
    I2C_1.enable();
    I2C_2.enable();
    I2C_3.enable();
    I2C_4.enable();
}

void HAL::SPI_init(void)
{
    RCC->APB2ENR |= RCC_APB2ENR_SPI1EN;

    SPI_1.configure(SPIMode::master, SPIDataSize::_8bits, SPIPolarity::idle_high, SPIPhase::data_on_second_edge, SPIForamt::MSB_first);
}

void HAL::GPIO_Init(void)
{
    /* Clock enable */
    RCC->AHB2ENR |= RCC_AHB2ENR_GPIOAEN;  // Enable clock for GPIOA
    RCC->AHB2ENR |= RCC_AHB2ENR_GPIOBEN;  // Enable clock for GPIOB
    RCC->AHB2ENR |= RCC_AHB2ENR_GPIOCEN;  // Enable clock for GPIOC
    RCC->AHB2ENR |= RCC_AHB2ENR_GPIOEEN;  // Enable clock for GPIOE

    I2C1_SCL.set_as_I2C_pin(eAF4);
    I2C1_SDA.set_as_I2C_pin(eAF4);

    I2C2_SCL.set_as_I2C_pin(eAF4);
    I2C2_SDA.set_as_I2C_pin(eAF4);

    I2C3_SCL.set_as_I2C_pin(eAF4);
    I2C3_SDA.set_as_I2C_pin(eAF4);

    I2C4_SCL.set_as_I2C_pin(eAF5);
    I2C4_SDA.set_as_I2C_pin(eAF5);

    SPI1_MISO.set_as_SPI_pin(eAF5);
    SPI1_MOSI.set_as_SPI_pin(eAF5);
    SPI1_SCK.set_as_SPI_pin(eAF5);

    SPI1_CS1.set_mode(eOutput);
    SPI1_CS1.set_output_type(ePushPull);
    SPI1_CS1.set_pullUp_pullDown(eNone);

    SPI1_CS2.set_mode(eOutput);
    SPI1_CS2.set_output_type(ePushPull);
    SPI1_CS2.set_pullUp_pullDown(eNone);

    SPI1_CS3.set_mode(eOutput);
    SPI1_CS3.set_output_type(ePushPull);
    SPI1_CS3.set_pullUp_pullDown(eNone);

    QSPI_IO0.set_as_SPI_pin(eAF10);
    QSPI_IO1.set_as_SPI_pin(eAF10);
    QSPI_IO2.set_as_SPI_pin(eAF10);
    QSPI_IO3.set_as_SPI_pin(eAF10);
    QSPI_CLK.set_as_SPI_pin(eAF10);
    QSPI_CS.set_as_SPI_pin(eAF10);

    UART3_RX.set_as_SPI_pin(eAF7);  // ToDo not spi :)
    UART3_TX.set_as_SPI_pin(eAF7);

    UART4_RX.set_as_SPI_pin(eAF7);  // ToDo not spi :)
    UART4_TX.set_as_SPI_pin(eAF7);

    BUTTON1.set_mode(eInput);
    BUTTON1.set_pullUp_pullDown(eNone);

    BUTTON2.set_mode(eInput);
    BUTTON2.set_pullUp_pullDown(eNone);

    BUTTON3.set_mode(eInput);
    BUTTON3.set_pullUp_pullDown(eNone);

    BUTTON4.set_mode(eInput);
    BUTTON4.set_pullUp_pullDown(eNone);
}

void HAL::DMA_init()
{
    RCC->AHB1ENR |= ((1 << 0) | (1 << 1));
}

void HAL::Timer_init()
{
    RCC->APB1ENR1 |= (1 << 0);

    Timer2.set_relode_value(625);    // 625
    Timer2.set_prescaler_value(79);  // 79
    Timer2.enable();
}

void HAL::NVIC_init(void)
{
    NVIC_EnableIRQ(DMA1_Channel2_IRQn);
    NVIC_EnableIRQ(DMA1_Channel4_IRQn);
    NVIC_EnableIRQ(DMA2_Channel7_IRQn);
    NVIC_EnableIRQ(DMA2_Channel2_IRQn);
    NVIC_EnableIRQ(TIM2_IRQn);
}

void HAL::TLC59208F_init(void)
{
    uint8_t first[] = {0, 0x08};
    uint8_t second[] = {0xAA, 0xAA};

    TLC59208F_1.init();
    TLC59208F_2.init();
    TLC59208F_3.init();
    TLC59208F_4.init();

    TLC59208F_1.set_registers_values(0x00, first, 2);
    TLC59208F_2.set_registers_values(0x00, first, 2);
    TLC59208F_3.set_registers_values(0x00, first, 2);
    TLC59208F_4.set_registers_values(0x00, first, 2);

    TLC59208F_1.set_registers_values(0x0C, second, 2);
    TLC59208F_2.set_registers_values(0x0C, second, 2);
    TLC59208F_3.set_registers_values(0x0C, second, 2);
    TLC59208F_4.set_registers_values(0x0C, second, 2);
}

void HAL::SR_74HC595_init(void)
{
    SR_74HC595_1.init();
    for (uint8_t i = 0; i < 32; i++)
        SR_74HC595_1.shift_bit(eHigh);
}

void HAL::LSM9DS1_init()
{
    LSM9DS1_1.init();

    LSM9DS1_1.set_data_rate(MagnetometerDataRate::Hz_80);
    LSM9DS1_1.set_XY_operation_mode(MagnetometerXYOperationMode::ultra_perforamnce);
    LSM9DS1_1.set_full_scale(MagnetometerFullScale::Gs_16);
    LSM9DS1_1.set_operation_mode(MagnetometerOperationMode::continuous_conversion);
}
