ProrokWielki/Wooden-Clock/Software/STM/src/stm32/HAL/Clock/Clock.cpp

/**
 * @file Clock.cpp
 * @author Pawel Warzecha
 * @brief
 * @version 0.1
 * @date 2025-02-26
 *
 * @copyright Copyright (c) 2025
 *
 */
#include <cassert>

#include <HAL/Register.hpp>
#include <HAL/types.hpp>
#include <cstdint>

#include "cmsis_bridge/cmsis_bridge.hpp"
#include "include/HAL/Clock.hpp"

Clock::Clock()
: AHB1(to_address(ClockRegister::AHB1)), AHB2(to_address(ClockRegister::AHB2)), AHB3(to_address(ClockRegister::AHB3)),
  APB1_1(to_address(ClockRegister::APB1_1)), APB1_2(to_address(ClockRegister::APB1_2)), APB2(to_address(ClockRegister::APB2)),
  PLL_CONFIG(to_address(ClockRegister::PLL_CONFIG)), CCIPR(to_address(ClockRegister::CCIPR)), CCIPR2(to_address(ClockRegister::CCIPR2)),
  BDCR(to_address(ClockRegister::BDCR)), CR(to_address(ClockRegister::CR)), CSR(to_address(ClockRegister::CSR)), CFGR(to_address(ClockRegister::CFGR))
{
}

void Clock::enable_clock_source(ClockSource clock_source)
{
    Register<uint32_t> & clock_source_register{get_clock_source_register(clock_source)};

    clock_source_register.set_bit(to_enable_bit_position(clock_source));

    wait_for_clock_source_to_be_ready(clock_source);
}

void Clock::enable_clock_for(Peripheral peripheral)
{
    Register<uint32_t> & peripheral_clock_register{get_peripheral_clock_register(peripheral)};

    peripheral_clock_register.set_bit(to_bit_position(peripheral));
}

void Clock::enable_pll()
{
    constexpr uint8_t PLL_ENABLE_BIT{24};
    PLL_CONFIG.set_bit(PLL_ENABLE_BIT);
}

void Clock::set_clock_source_for(PeripheralWithSelectableClockSource peripheral, ClockSource clock_source)
{
    assert(is_clock_source_supported(peripheral, clock_source) && "Unsupported clock source.");

    Register<uint32_t> & peripheral_clock_source_register{get_peripheral_clock_source_register(peripheral)};
    peripheral_clock_source_register.set_value(to_clock_source_value(peripheral, clock_source), to_clock_source_position(peripheral),
                                               to_peripheral_clock_select_field_length(peripheral));
}

void Clock::set_system_clock_source(ClockSource clock_source)
{
    assert(is_system_clock_source_supported(clock_source) && "Unsupported clock source.");

    constexpr uint8_t SYSTEM_CLOCK_SWITCH_FIELD_LENGTH{2};
    constexpr uint8_t SYSTEM_CLOCK_SWITCH_BIT_POSITION{0};
    CFGR.set_value(to_system_clock_source_value(clock_source), SYSTEM_CLOCK_SWITCH_BIT_POSITION, SYSTEM_CLOCK_SWITCH_FIELD_LENGTH);
}

void Clock::set_pll_clock_source(ClockSource clock_source)
{
    assert(is_pll_clock_source_supported(clock_source) && "Unsupported clock source.");

    constexpr uint8_t PLL_CLOCK_SOURCE_BIT_POSITION{0};
    constexpr uint8_t PLL_CLOCK_SOURCE_FIELD_LENGTH{2};
    PLL_CONFIG.set_value(to_pll_clock_source_value(clock_source), PLL_CLOCK_SOURCE_BIT_POSITION, PLL_CLOCK_SOURCE_FIELD_LENGTH);
}

void Clock::set_pll_factors(uint32_t m, uint32_t n, uint32_t r, uint32_t p, uint32_t q)
{
    PLL_CONFIG.set_value(m - 1, 4, 3);
    PLL_CONFIG.set_value(n, 8, 7);
    PLL_CONFIG.set_value(r == 2 ? 0 : (r == 4 ? 1 : (r == 6 ? 2 : 3)), 25, 2);
    PLL_CONFIG.set_value(p == 7 ? 0 : 1, 18, 1);
    PLL_CONFIG.set_value((q == 2) ? 0 : ((q == 4) ? 1 : ((q == 6) ? 2 : ((q == 8) ? 3 : 0))), 21, 2);
}

[[nodiscard]] uint32_t Clock::get_clock_frequency() const
{
    constexpr uint32_t CLOCK_FREQUENCY{80'000'000};  // TODO: Get from RCC->CFGR
    return CLOCK_FREQUENCY;
}

void Clock::reset_backup_domain()
{
    static constexpr uint8_t BACKUP_DOMAIN_RESET_BIT{16};

    BDCR.set_bit(BACKUP_DOMAIN_RESET_BIT);
    BDCR.clear_bit(BACKUP_DOMAIN_RESET_BIT);
}

void Clock::wait_for_clock_source_to_be_ready(ClockSource clock_source)
{
    while (not is_clock_source_ready(clock_source))
        ;
}

bool Clock::is_clock_source_ready(ClockSource clock_source)
{
    const Register<uint32_t> & clock_source_register{get_clock_source_register(clock_source)};

    return clock_source_register.get_bit(to_ready_bit_position(clock_source));
}

Register<uint32_t> & Clock::get_peripheral_clock_register(Peripheral peripheral)
{
    switch (peripheral)
    {
        case Peripheral::EXTERNAL_FLASH:
        case Peripheral::DMA_2:
        case Peripheral::DMA_1:
        case Peripheral::TOUCH_SENSE:
        case Peripheral::CRC_UNIT:
            return AHB1;
        case Peripheral::ADC:
        case Peripheral::AES:
        case Peripheral::RANDOM_NUMBER_GENERATOR:
        case Peripheral::GPIO_A:
        case Peripheral::GPIO_B:
        case Peripheral::GPIO_C:
        case Peripheral::GPIO_D:
        case Peripheral::GPIO_E:
        case Peripheral::GPIO_H:
            return AHB2;
        case Peripheral::QSPI:
            return AHB3;
        case Peripheral::LOW_POWER_TIMER_1:
        case Peripheral::OP_AMP:
        case Peripheral::DAC_1:
        case Peripheral::USB_FS:
        case Peripheral::CAN_1:
        case Peripheral::I2C_1:
        case Peripheral::I2C_2:
        case Peripheral::I2C_3:
        case Peripheral::USART_2:
        case Peripheral::USART_3:
        case Peripheral::UART_4:
        case Peripheral::SPI_3:
        case Peripheral::SPI_2:
        case Peripheral::TIMER_2:
        case Peripheral::TIMER_3:
        case Peripheral::TIMER_6:
        case Peripheral::TIMER_7:
        case Peripheral::LCD:
        case Peripheral::WINDOW_WATCHDOG:
        case Peripheral::CLOCK_RECOVERY_SYSTEM:
        case Peripheral::POWER_INTERFACE:
        case Peripheral::RTC_APB:
            return APB1_1;
        case Peripheral::LOW_POWER_TIMER_2:
        case Peripheral::I2C_4:
        case Peripheral::LOW_POWER_UART_1:
        case Peripheral::SINGLE_WIRE:
            return APB1_2;
        case Peripheral::USART_1:
        case Peripheral::SPI_1:
        case Peripheral::TIMER_1:
        case Peripheral::TIMER_15:
        case Peripheral::TIMER_16:
        case Peripheral::SDMMC_1:
        case Peripheral::FIRE_WALL:
        case Peripheral::SAI_1:
        case Peripheral::DFSDM_1:
        case Peripheral::SYSTEM_CONFIG:
            return APB2;
        case Peripheral::RTC_1:
            return BDCR;
        default:
            assert(false && "invalid peripheral");
            return APB1_1;
    };
}

Register<uint32_t> & Clock::get_clock_source_register(ClockSource clock_source)
{
    switch (clock_source)
    {
        case ClockSource::LSE:
            return BDCR;
        case ClockSource::HSE:
        case ClockSource::MAIN_PLL:
            return CR;
        case ClockSource::LSI:
            return CSR;
        case ClockSource::PCLK:
        case ClockSource::HSI16:
        case ClockSource::SYSTEM_CLOCK:
        case ClockSource::MSI:
        case ClockSource::HSI48:
        case ClockSource::PCLK1:
        case ClockSource::PLL_ADC_CLOCK:
        case ClockSource::PLL_48_M1_CLOCK:
        case ClockSource::PLL_48_M2_CLOCK:
        case ClockSource::PLL_SAI_CLOCK:
        case ClockSource::PLL_P_CLOCK:
        case ClockSource::SAI_EXTERNAL_CLOCK:
            assert(false && "Not implemented.");
            return BDCR;
        default:
            assert(false && "invalid clock source");
            return BDCR;
    }
}

Register<uint32_t> & Clock::get_peripheral_clock_source_register(PeripheralWithSelectableClockSource peripheral)
{
    switch (peripheral)
    {
        case PeripheralWithSelectableClockSource::USART_1:
        case PeripheralWithSelectableClockSource::USART_2:
        case PeripheralWithSelectableClockSource::USART_3:
        case PeripheralWithSelectableClockSource::UART_4:
        case PeripheralWithSelectableClockSource::LOW_POWER_UART_1:
        case PeripheralWithSelectableClockSource::I2C_1:
        case PeripheralWithSelectableClockSource::I2C_2:
        case PeripheralWithSelectableClockSource::I2C_3:
        case PeripheralWithSelectableClockSource::ADC:
        case PeripheralWithSelectableClockSource::CLK_48MHZ:
        case PeripheralWithSelectableClockSource::LOW_POWER_TIMER_1:
        case PeripheralWithSelectableClockSource::LOW_POWER_TIMER_2:
        case PeripheralWithSelectableClockSource::SINGLE_WIRE:
        case PeripheralWithSelectableClockSource::SAI_1:
            return CCIPR;
        case PeripheralWithSelectableClockSource::I2C_4:
            return CCIPR2;
        case PeripheralWithSelectableClockSource::RTC_1:
            return BDCR;
        default:
            assert(false && "invalid peripheral");
            return CCIPR;
    }
}
