ProrokWielki/Wooden-Clock/Software/STM/tests/hil/gpio_test/test_gpio.py

def test_gpio(expectations):    
    for output in expectations:
        expectation_line = output[0]
        lhs = output[1][0]
        rhs = output[1][1]
        
        assert lhs == rhs, f"{expectation_line} expected {lhs} == {rhs}"
